timbod7/gps-tracker/docs/IMG_0564.JPEG

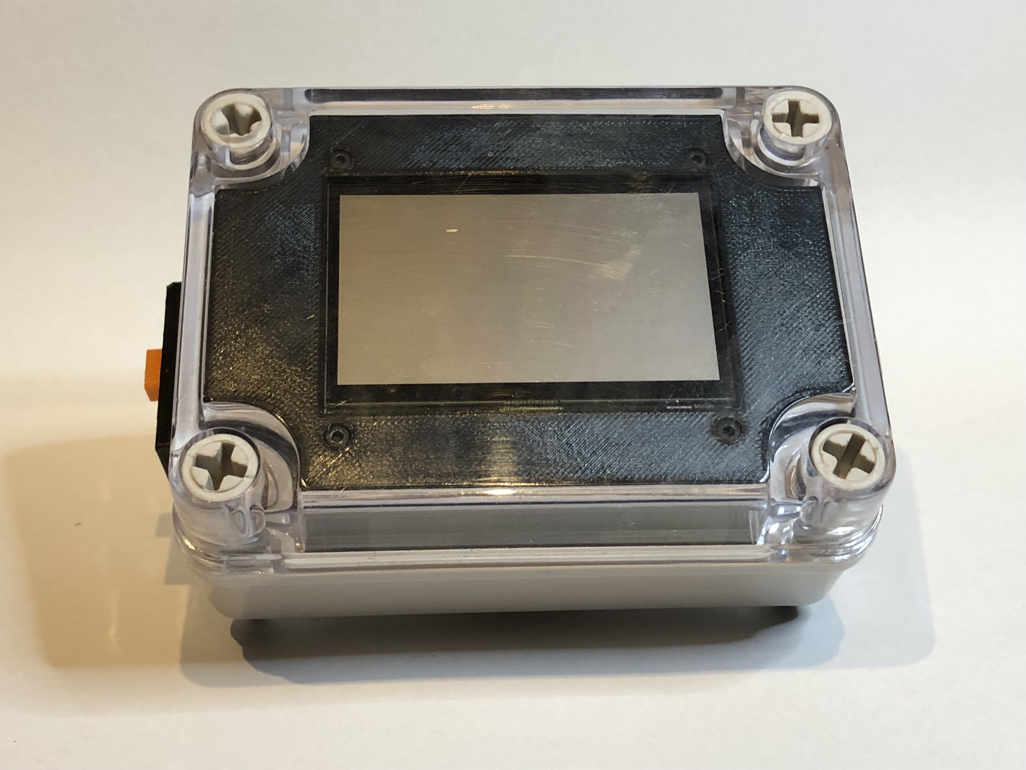
docs/IMG_0564.JPEG
